MaZderMind/microdrum/Software/Firmware/midi.c

/**
 * @file
 * Ansteuerung eines MIDI-Gerätes über den UART-Controller
 */

#include <stdlib.h>
#include <string.h>
#include <avr/io.h>
#include <avr/interrupt.h>

#include "bits.h"
#include "io_config.h"
#include "midi.h"

/**
 * Pointer zum gespeicherten Clock-Interrupt-Callback
 */
volatile midi_clock_handler clock_callback;

// TODO: in eine Struct verpacken
typedef struct {
	// Clock-Interrupt pausiert
	unsigned paused:1;

	// gespeicherter Clock-Prescaler
	unsigned prescale:7;

	// Clock-Counter-Reset, abgeletitet von der gewünschten Beats-Zahl
	uint8_t reset;

	// Zähler der interupt-routine
	uint8_t clk;

	// Auf Daten wartendes Kommando
	uint8_t last_command;

	// Anzahl der fehlenden Bytes
	uint8_t bytes_required;

	// Daten des Kommandos
	uint8_t data_bytes[3];
} midi_clock_interrupt_state_t;

volatile midi_clock_interrupt_state_t midi_clock_interrupt_state;

/**
 * 8-Bit-Feld zum speichern der derzeit aktiven Instrumente
 */
uint8_t midi_triggered_instruments = 0;

/**
 * Die Midi-Kommunikation initialisieren
 */
void midi_init(void)
{
	// BAUD-Konstante auf den Wert von MIDI_BAUD setzen
	#undef BAUD
	#define BAUD MIDI_BAUD

	// setbaud.h laden, welches die UART-Prescaler-Werte anhand des
	// CPU-Taktes errechnet
	#include <util/setbaud.h>

	// Die Baudrate High/Low setzen, welche in setbaud.h errechnet wurde
	UBRRH = UBRRH_VALUE;
	UBRRL = UBRRL_VALUE;

	// wenn nötig, aktivierung des 2X Modus
	#if USE_2X
		SETBIT(UCSRA, U2X);
	#else
		CLEARBIT(UCSRA, U2X);
	#endif

	// Asynchron 8N1 (8 Datenbits, keine Parität, 1 Stop-Bit)
	SETBITS(UCSRC, BIT(URSEL) | BIT(UCSZ0) | BIT(UCSZ1));

	// Das TransmitEnable-Bit und das ReceiveEnable-Bit im UartControlAndStatusRegisterB setzen
	SETBITS(UCSRB, BIT(TXEN) | BIT(RXEN));

	// Status nullen
	memset((void*)&midi_clock_interrupt_state, 0, sizeof(midi_clock_interrupt_state_t));
}

/*
 * Doku wird vom Header-File übernommen
 */
void midi_set_clock_interrupt(midi_clock_handler cb, uint8_t prescale, uint8_t beats)
{
	// Das ReceiveCompleteInterruptEnable im UartControlAndStatusRegisterB setzen
	SETBIT(UCSRB, RXCIE);

	// Interupts global aktivieren
	sei();

	// Den callback speichern
	clock_callback = cb;

	// Den Prescaler speichern
	midi_clock_interrupt_state.prescale = prescale;

	// Die Beats-Zahl speichern
	midi_clock_interrupt_state.reset = prescale * beats;
}

/**
 * Midi-Daten über den UART übermitteln
 */
void midi_send(uint8_t data)
{
	//  warten bis Senden möglich ist
	while(BITCLEAR(UCSRA, UDRE));

	// Daten senden
	UDR = data;
}

/*
 * Ein Instrument triggern
 * siehe Header-Datie für mehr Informationen
 */
void midi_trigger_instrument(uint8_t instrument, uint8_t velocity)
{
	// NoteOn-Nachricht senden
	midi_noteon(midi_instruments[instrument], velocity);

	// das entsprechende Bit im Bitfeld setzen
	SETBIT(midi_triggered_instruments, instrument);
}


/*
 * Alle zuvor aktiven Instrumente deaktivieren
 * siehe Header-Datie für mehr Informationen
 */
void midi_detrigger_instruments(void)
{
	// für alle Instrumente
	for(uint8_t instrument = 0; instrument < N_INSTRUMENTS; instrument++)
	{
		// Testen, ob das entsprechende Bit gesetzt ist
		if(BITSET(midi_triggered_instruments, instrument))
		{
			// und sende ggf. eine NoteOff-Nachricht
			midi_noteoff(midi_instruments[instrument]);
		}
	}

	// Das Bitfeld leeren
	midi_triggered_instruments = 0;
}

/*
 * Ein NoteOn-Kommando senden
 * siehe Header-Datie für mehr Informationen
 */
void midi_noteon(uint8_t note, uint8_t velocity)
{
	// Midi-Kanal senden
	midi_send((midi_channel & 0x0F) | MIDI_NOTEON);

	// Noten-Wert senden
	midi_send(note & 0x7F);

	// Anschlagstärke senden
	midi_send(velocity & 0x7F);
}

/*
 * Ein NoteOff-Kommando senden
 */
void midi_noteoff(uint8_t note)
{
	// Midi-Kanal senden
	midi_send((midi_channel & 0x0F) | MIDI_NOTEOFF);

	// Noten-Wert senden
	midi_send(note & 0x7F);

	// Anschlagstärke 0 senden
	midi_send(0);
}

/*
 * Eine Midi-Controll-Change-Nachricht senden
 */
void midi_cc(uint8_t controller, uint8_t value)
{
	// Midi-Kanal senden
	midi_send((midi_channel & 0x0F) | MIDI_CC);

	// Controller-Nummer
	midi_send(controller & 0x7F);

	// Controller-Wert
	midi_send(value & 0x7F);
}


/**
 * Den Namen einer Note zusammenbauen
 * Gibt einen Pointer auf einen statischen Speicherbereich zurück, der
 * gültig bleibt, bis die Methode erneut aufgerufen wird.
 *
 *  Midi-Note 0  =  C -1
 *            1  =  C#-1
 *            2  =  D -1
 *              ...
 *          125  =  F 9
 *          126  =  F#9
 *          127  =  G 9
 */
const char* midi_notename(uint8_t note)
{
	// statischer String-Puffer von 6 Bytes
	//  3 Bytes für den Notennamen (siehe midi.h)
	//  2 Bytes für die Oktave (-1 bis 9)
	//  1 Null-Byte (Stringende)
	static char notename[6] = "";

	// Index der Basisnote (C-B ? 0-11)
	uint8_t basenote = note % 12;

	// Name der Note aus dem Namen-Array kopieren
	strcpy(notename, midi_notenames[basenote]);

	// Postfix der Note (-1 bis 9)
	int8_t postfix = (note / 12) - 1;

	// Postix in einen String umwandeln
	char postfix_str[3] = "";
	itoa(postfix, postfix_str, 10);

	// an den Notennamen anhängen
	strcat(notename, postfix_str);

	// Pointer auf statisches Array zurückgeben
	return notename;
}

/**
 * Midi 2-Byte-Nachrichten (z.B. Pitch-Wheel oder SongPositionPointer) zusammensetzen
 */
uint16_t midi_combine_bytes(uint8_t first, uint8_t second)
{
	uint16_t _14bit;

	_14bit = (uint16_t)second;
	_14bit <<= 7;
	_14bit |= (uint16_t)first;

	return _14bit;
}

uint8_t midi_process_realtime(uint8_t input, midi_clock_interrupt_state_t *state)
{
	switch(input)
	{
		// Eine Clock-Nachricht
		case MIDI_CLOCK: {
			if(state->paused)
				return 1;

			// Wenn der Prescaler erreicht wurde
			if(state->clk % state->prescale == 0)
			{
				// den Event-Handler auslösen, dabei den passenden Beat ausrechnen
				if(clock_callback)
					clock_callback(state->clk / state->prescale);
			}

			// Den Clock-Zähler erhöhen, dabei prüfen ob die max. Beat-Zahl erreicht wurde
			if(++state->clk == state->reset)
			{
				// Den Clock-Zähler zurück setzen
				state->clk = 0;
			}
			return 1;
		}

		// Eine MIDI-Start-Nachricht setzt den Clock-Zähler auf 0 zurück
		// und aktiviert den Clock-Zähler
		case MIDI_START: {
			// Den Clock-Zähler auf 0 zurück fahren
			state->clk = 0;
			state->paused = 0;
			return 1;
		}

		// Eine MIDI-Stop-Nachricht stoppt den Clock-Zähler
		case MIDI_STOP: {
			state->paused = 1;
			return 1;
		}

		// Eine MIDI-Ĉontinue-Nachricht aktiviert den Clock-Zähler
		case MIDI_CONTINUE: {
			state->paused = 0;
			return 1;
		}
	}

	// Dies war keine Realtime-Nachricht
	return 0;
}



uint8_t midi_process_data(uint8_t input, midi_clock_interrupt_state_t *state)
{
	// eine wartende Nachricht
	if(state->last_command > 0)
	{
		// Ein weiteres Byte dieser Nachricht empfangen
		state->data_bytes[state->bytes_required] = input;

		// Alle benötigten Bytes für diese Nachricht wurden empfangen
		if(state->bytes_required == 0)
		{
			// Empfangene Nachricht verarbeiten
			switch(state->last_command)
			{
				// eine SPP-Nachricht
				case MIDI_SONG_POSITION_POINTER: {
					// empfangene Bytes zu Midi-Beats zusammenführen
					uint16_t spp = midi_combine_bytes(state->data_bytes[1], state->data_bytes[0]);

					// jeder Midi-Beat entspricht 6 Clock-Cycles,
					// welche dann auf die Länge des internen Sequenzers umgelegt wird
					state->clk = (spp * 6) % state->reset;
				}
			}

			// wartendes Kommando wurde abgearbeitet
			state->last_command = 0;
		}

		// sonst die Anzahl der benötigten Bytes reduzieren
		else state->bytes_required--;

		// Es wurde ein Datenbyte verarbeitet
		return 1;
	}

	// Keine wartetende Nachricht
	return 0;
}


uint8_t midi_process_message(uint8_t input, midi_clock_interrupt_state_t *state)
{
	// Nachricht auswerten
	switch(input)
	{
		case MIDI_SONG_POSITION_POINTER: {
			state->last_command = MIDI_SONG_POSITION_POINTER;
			state->bytes_required = 1; // 2 Bytes

			return 1;
		}

#if 0
		case MIDI_SONG_SELECT: {
			// select saved pattern via Callback
			state->clk = 0;
			return 1;
		}
#endif
	}

	// Keine verarbeitete Nachricht
	return 0;
}






/**
 * UART Empfangs-Interrupt
 */
ISR(USART_RXC_vect)
{
	// anliegende Nachricht aus dem Puffer lesen
	uint8_t input = UDR;

	// State aus dem RAM lesen
	midi_clock_interrupt_state_t state = midi_clock_interrupt_state;


	// Realtime-Nachrichten verarbeiten (können zu jedem Zeitpunkt auftreten)
	if(!midi_process_realtime(input, &state))
	{
		// Daten von Mehrteil-Nachrichten verarbeiten
		if(!midi_process_data(input, &state))
		{
			// Kommando-Nachrichten verarbeiten
			midi_process_message(input, &state);
		}
	}

	// State zurück in den RAM schreiben
	 midi_clock_interrupt_state = state;
}
