MaZderMind/microdrum/Software/Firmware/io.c

/**
 * @file
 * Ansteuerung der Peripherie
 */

#include <stdint.h>
#include <avr/io.h>
#include <util/delay.h>
#include "bits.h"
#include "lcd.h"
#include "io.h"
#include "io_parameter.h"
#include "io_selector.h"
#include "io_sequencer.h"

/*
 * Die Peripherie initialisieren
 */
void io_init(void)
{
	// Mux-Lines auf Ausgang
	SETBITS(MUX_DDR, BIT(MUX_PIN0) | BIT(MUX_PIN1) | BIT(MUX_PIN2));

	// Sync-Timer-Pin auf Ausgang
	SETBIT(TIMER_DDR, TIMER_PIN);

	// Initialisieren der Parameter-Boards
	io_parameter_init();

	// Initialisieren der Sequencer-Boards
	io_sequencer_init();

	// Initialisieren des Selektorrades
	io_selector_init();
}

/**
 * Die Multiplexer auf einen anderen Kanal umschalten
 */
void io_select(uint8_t channel)
{
	// Die drei Multiplexer-Pins auf 1 schalten
	CLEARBITS(MUX_PORT, BIT(MUX_PIN0) | BIT(MUX_PIN1) | BIT(MUX_PIN2));

	// Die Kanalwahl auf 3 Bits beschränken und auf die Multiplexer-Pins legen
	MUX_PORT |= ((channel & 0x07) << MUX_PIN);

	// den Multiplexern Zeit zum Umschalten geben
	_delay_us(1);
}

/*
 * Die Peripherie mit dem internen Zustand synchronisieren
 */
void io_sync(void)
{
	// Sync-Timer-Led umschalten
	TOGGLEBIT(TIMER_PORT, TIMER_PIN);

	// Alle 8 Multiplexer-Zustände ablaufen
	for(uint8_t cycle = 0; cycle < 8; cycle++)
	{
		// Tastendrücke und Rad-Drehung detektieren
		// TODO: ggf. aus dem loop rausnehmen
		io_selector_detect();

		// Sequencer Leds ausschalten
		io_sequencer_presync(cycle);

		// Multiplexer umschalten
		io_select(cycle);

		// Sequencer Leds ggf. wieder an schalten und und Taster detektieren
		io_sequencer_sync(cycle);

		// Werte der Parameter-Boards auslesen
		io_parameter_sync(cycle);
	}
}
