MaZderMind/microdrum/Software/MidiDemo1/MidiDemo1/midi.h

/**
 * Ansteuerung eines MIDI-Gerätes über den UART-Controller
 *
 * http://arduino.cc/en/Tutorial/Midi
 * http://www.mikrocontroller.net/articles/UART
 */

#ifndef MIDI_H_
#define MIDI_H_

/**
 * Baudrate der MIDI-Kommunikation
 */
#define MIDI_BAUD 31250UL

/**
 * Benennung der 12 Noten
 */
static const char* const midi_notenames[] = {"C ", "C#", "D ", "D#", "E ", "F ", "F#", "G ", "G#", "A ", "A#", "B "};

/**
 * Die Midi-Kommunikation initialisieren
 */
void midi_init();

/**
 * Ein NoteOn-Kommando senden
 */
void midi_noteon(uint8_t channel, uint8_t note, uint8_t velocity);

/**
 * Ein NoteOff-Kommando senden
 */
void midi_noteoff(uint8_t channel, uint8_t note);

/**
 * Den Namen einer Note zusammenbauen
 */
const char* midi_notename(uint8_t note);

#endif /* MIDI_H_ */
